A622266/NZIF_Radio/nzif/docs/NZIF_Radio_System_Architecture_Schematic_Review_2026-06-06.odt

NZIF Radio — System Architecture & Full Schematic Review

Review Date: 2026-06-06 | Scope: All schematic sheets, mixer-to-DSP core | Status: HOLD — Critical items block layout freeze

# 1. Executive Summary

This review covers the complete NZIF Radio schematic at the mixer-to-DSP level. Six domain expert reviews were conducted in parallel across all twelve schematic sheets. The design represents a genuinely novel 8-phase near-zero-IF architecture that is publishable in principle. However, the schematic has 11 Critical issues (up from 9 in the prior review), 25+ High issues, and numerous Moderate findings that must be resolved before layout or fabrication. Hardware does not yet exist; all performance figures are theoretical estimates requiring bring-up validation.

QST Verdict: The architecture deserves a QST article. The execution needs a complete schematic correction pass before that becomes possible. The minimum viable path to a working prototype requires resolution of all Tier 1 critical items listed in Section 6.

## 1.1 Top Critical Issues — Must Fix Before Layout

# | Sheet | Issue | Risk

CRITICAL 1 | rx_mixer rx_driver_amps | Wrong lib_ids on all custom power symbols (power:+5V used for −3.5V, +6.5V rails) | Netlist shorts negative op-amp rail to +5V; ADG884 destroyed on power-up
CRITICAL 2 | power_ldos | R903/R907/R908/R909 missing 'k' suffix (49.9 Ω not 49.9 kΩ) | All four LDO rails produce ~5 mV; complete subsystem failure
CRITICAL 3 | power_switching_reg | LT8330 feedback R1101/R1102 wrong values (produces −1.79V not −5V) | −5V rail absent; analog op-amp supply fails
CRITICAL 4 | power_switching_reg | ADP2303 R1103/R1104 wrong values (1.6V not target voltage) | Target rail at wrong voltage; dependent LDOs receive wrong input
CRITICAL 5 | clock_tree | R701 = 1 kΩ on OSC_CTRL; AD9523-1 requires ≥20 kΩ load (total 11 kΩ) | VCXO PLL1 will not lock; radio is inoperable without reference clock
CRITICAL 6 | clock_tree | U706 symbol=SN74CBT3253 (5V) vs. Value=SN74CBTLV3253 (3.6V max) | Wrong device assembled; 3.6V-max part destroyed at 5V supply
CRITICAL 7 | dacs | ADAU1962A AVDD driven from Q601 emitter follower: ~2.7V vs. 3.0V minimum | DAC internal references out of spec; possible startup failure
CRITICAL 8 | adcs audio_subsystem | Power symbol lib_id power:+3.3V used for +3.3V_CONVERTERS — merges with global +3.3V | ADC and ADAU1361 analog supply contaminated by digital noise; isolation defeated
CRITICAL 9 | audio_subsystem | Power symbol lib_id power:+5V for +3.3V_CONVERTERS — applies 5V to ADAU1361 IOVDD/AVDD (3.6V abs max) [NEW] | ADAU1361 destroyed on first power-up
CRITICAL 10 | audio_subsystem | Net label 'DVDOUT' should be 'DVDDOUT'; ADAU1361 internal LDO decoupling disconnected | Codec internal digital supply unstable; codec non-functional
CRITICAL 11 | adcs | ADAU1979 PLL_FILT cap C406 (5600 pF) marked DNP [NEW] | ADC internal PLL cannot lock; ADU1979 completely non-functional

# 2. System Architecture Assessment

## 2.1 Architecture Strengths

8-Phase Polyphase Mixer — Genuine Novelty: The 8-phase commutating topology with SN74CBT3125C bus switches provides theoretical >60 dB rejection of the 3rd LO harmonic, >50 dB of the 5th, and >45 dB of the 7th. No published amateur construction project has implemented this. The mathematics (8-point DFT phasor argument) is correct and is validated by the rxmixer.md simulation showing correct 45° phase spacing and matched amplitudes. This directly surpasses Tayloe's 4-phase detector (QEX, May 2001) and is the primary novelty claim for a QST article.

AD9523-1 Dual-Output Clock Architecture: Generating both the variable RF LO and the fixed audio MCLK from a single VCO, with the reference-path divider completely decoupled from PLL2 tuning, is architecturally elegant. Retuning the LO does not disturb the I2S clock domain — a non-trivial design insight that most amateur SDR designs get wrong. The AD9523-1's −226 dBc/Hz FOM is appropriate for a receiver targeting superheterodyne-class phase noise performance.

Ring Counter Phase Generation: The SN74AUC16374 ring counter producing eight non-overlapping phase pulses from a circulating single-bit shift register is original and elegant. The 4:1 mux initialisation sequence (clear → seed → run) reproducibly places exactly one '1' in the loop, solving the undefined power-up state problem without external reset logic. The 2.5V supply choice allows 237.6 MHz operation for 10m (8-phase) within the 250 MHz typical device rating.

Fully Differential Signal Flow: The receive chain is fully differential from the balun secondary through SN74CBT3125C switches → ADA4625-2 buffers → ADA4945-1 FDAs → ADAU1979 ADC. Maintaining differential mode throughout suppresses even-order nonlinearities and rejects common-mode RF interference. The LT5400 matched quad resistors for ADA4945-1 Rg positions (0.01% ratio matching, 0.5 ppm/°C tracking) are the right call for I/Q amplitude balance.

Near-Zero-IF + NCO Strategy: The ADAU1467 digital NCO (±96 kHz) offsets the receive center from DC, avoiding LO leakage and 1/f noise without a switched IF filter bank. Combined with 100 kHz LO steps from the AD9523-1, this provides continuous HF coverage. The Weaver two-stage demodulation (first stage: analog 8-phase mixer; second stage: digital NCO in ADAU1467) is a legitimate and clean implementation.

LT3045/LT3094 Power Architecture: The use of ultra-low-noise LDOs (2 µVrms) post-regulating from ADP2302/ADP2303 switchers, with domain-isolated rails for the clock tree, mixers, and audio converters, reflects serious attention to the ADC noise floor. The LT3045's 76 dB PSRR at 1 MHz directly addresses 700 kHz switcher ripple. This is a publishable design decision that most commercial SDR kits do not implement.

I/Q Calibration Architecture: The directional coupler calibration tap + HMC1118 switch injecting a known spectrally clean signal into the receive path for runtime I/Q calibration goes beyond any published amateur receiver design. If implemented correctly, this allows image rejection to be maintained across temperature and band changes without manual trimming.

ADAU1467 SigmaDSP Integration: The 294 MHz dual-core ADAU1467 running SigmaStudio graphical blocks (NCO, Weaver second stage, FIR/IIR filters, AGC, I/Q correction matrix) provides more DSP headroom than a comparably priced FPGA for audio-rate processing, without requiring custom firmware. I2C parameter RAM access from the Pico enables runtime calibration coefficient updates.

## 2.2 Architecture Concerns

TX Reconstruction Filter Absent [CRITICAL]: The tx_mixer.kicad_sch sheet title promises '16 Phase Tx Harmonic Mixer and Reconstruction Filter' but contains no filter components. DAC reconstruction images at LO ± 192 kHz and harmonics feed directly to the PA interface. The ZWAS LPF on the RF front-end board suppresses PA harmonics but not pre-PA mixer images. A fully differential LC filter at TX_RF+/TX_RF- is required before FCC Part 97 compliance can be claimed.

Hold Capacitor Values Produce ~4 kHz Baseband Bandwidth [NEW HIGH]: The rx_mixer annotation uses N=1 in the bandwidth equation; the correct value for an 8-phase topology is N=8. With 100 nF hold caps and Reff ≈ 50 Ω source / N=8: BW ≈ 1/(2π × 8 × 50 × 100 nF) ≈ 4 kHz. This is far below the ±96 kHz NCO range. For ±200 kHz bandwidth target: C_hold ≈ 2 nF. The current 100 nF caps limit the design to CW-only operation, inconsistent with the stated SSB/AM/digital mode goals.

VCXO vs. TCXO Conflict [NEW HIGH]: CLAUDE.md and the architecture description state CTS_535_TCXO as the frequency reference, but clock_tree.kicad_sch instantiates an ABLNO-V-VCXO. These are functionally different devices. The AD9523-1 is designed for a VCXO reference on PLL1 (OSC_CTRL drives Vc), which makes the ABLNO-VCXO the architecturally correct choice — but the documentation and schematic disagree. This must be resolved explicitly.

6m 4-Phase Mode Spurious Response: In 4-phase mode (6m), the 5th harmonic (f_LO/5 ≈ 10–10.8 MHz = 30m band) passes through with the same response vector as the fundamental. HP-2 (9 MHz cutoff) provides only modest attenuation at 10 MHz. Strong 30m signals will create interference on 6m. This limitation is inherent to 4-phase operation and should be quantified and disclosed in any QST article.

Power Sequencing Undefined: No PGOOD connections link switching regulator outputs to downstream LDO enable pins. The ADAU1467 requires DVDD and IOVDD within 0.3 V of each other during power-up to prevent latch-up. All rails currently rise simultaneously with no defined order. ADP2303 PGOOD pins have no pull-up resistors.

ADA4945-1 Feedback Caps All DNP: All eight 180 pF feedback capacitors across the ADA4945-1 Rf resistors are marked DNP. With Rf = 9.53 kΩ and no Cf, the ADA4945-1 will oscillate on first prototype, saturating all four differential channels and making the ADC input useless. These must be populated.

## 2.3 QST Readiness Assessment

Strengths for publication: The 8-phase polyphase mixer topology is a publishable concept that advances the state of amateur radio construction. The dual-path clock architecture, ring counter phase generation, and I/Q calibration system are all novel and technically rigorous. The LTspice simulation validating the 45° phase spacing is a publication-ready figure. A QST reviewer familiar with Tayloe's detector would immediately recognise this as a significant advancement.

Blockers to publication: (1) 11 critical schematic errors that would prevent a built board from functioning. (2) No hardware exists — all performance figures are theoretical estimates. QST requires bench-measured data for all performance claims. (3) TX reconstruction filter absent — transmitter cannot claim Part 97 compliance. (4) Hold capacitor values inconsistent with stated ±96 kHz operating bandwidth. (5) Schematic net errors (power symbol lib_ids) that would destroy components on first power-up.

Recommended path to QST submission: Fix all Tier 1 critical items → build first prototype → measure MDS, IIP3, harmonic rejection (3rd/5th/7th), image rejection, and TX spectrum → submit with measured data and corrected ERC-clean schematic.

# 3. New Findings — This Review Cycle

The following issues were not in the prior schematic_review_report.md and were identified by this review cycle:

Priority | Sheet | Ref/Net | Issue | Action
CRITICAL [NEW] | audio_subsystem | +3.3V_CONVERTERS power symbol | lib_id 'power:+5V' with Value '+3.3V_CONVERTERS' applies 5V to ADAU1361 IOVDD/AVDD (abs max 3.6V) → device destroyed | Create dedicated power symbol with lib_id 'power:+3.3V_CONVERTERS'
CRITICAL [NEW] | adcs | C406 (PLL_FILT) | 5600 pF PLL_FILT cap is marked DNP. ADAU1979 internal PLL cannot lock without this capacitor → ADC non-functional | Populate C406; do not DNP on prototype
CRITICAL [NEW] | dacs | Net '2.5' (no V suffix) | Label '2.5' (missing 'V') at line 6617 creates a net isolated from all '2.5V' nets. Floating node risk at DAC reference | Rename to '2.5V'; verify no other case/suffix mismatches in DAC sheet
HIGH [NEW] | clock_tree | X701 vs ABLNO-VCXO | Architecture docs say CTS_535_TCXO; schematic instantiates ABLNO-V-VCXO. Fundamentally different parts (TCXO vs VCXO) | Commit to ABLNO-VCXO (architecturally correct for AD9523-1 PLL1); update CLAUDE.md; remove unused CTS_535 symbol
HIGH [NEW] | rx_mixer | HC_201–208 hold caps | Bandwidth annotation uses N=1 but topology has N=8 phases. Correct BW with 100 nF: ~4 kHz, not 96 kHz. Inconsistent with ±96 kHz NCO design goal | Recalculate for N=8: C_hold ≈ 2 nF for 200 kHz target BW; update annotation and fitted values
HIGH [NEW] | adcs | U401 VREF buffer | R410 (3kΩ) loads ADAU1979 VREF pin (unbuffered bandgap output) with 0.83 mA before the ADA4807-1 buffer — exceeds recommended loading | Move R410 to output of ADA4807-1 buffer, not input; ensure VREF pin sees only buffer input impedance
HIGH [NEW] | adcs | C401, C403 AVDD caps | 10 µF AVDD bypass caps assigned to 0402 footprint. DC bias derating at 3.3V reduces effective C to 3–5 µF (marginal). No 10 µF ceramic exists in 1005 metric | Change footprint to 0805; use 10 µF X5R/X7R 0805 rated ≥6.3V
HIGH [NEW] | dacs | Q601 / AVDD | FZT951TA emitter follower produces ~3.3V − 0.6V = 2.7V AVDD at room temp. Falls further with temperature. ADAU1962A AVDD minimum is 3.0V | Replace Q601 with LT3045 LDO; set output to 3.3V with correct SET resistor value
HIGH [NEW] | dsp | SELFBOOT / U502 EEPROM | SELFBOOT pin state unconfirmed. U502 (25AA1024 SPI EEPROM) footprint is empty — absent from layout. Self-boot path cannot function without EEPROM | Assign footprint to U502; confirm SELFBOOT pulled high (IOVDD); document boot mode in schematic note
HIGH [NEW] | tx_mixer | Tx DAC differential polarity | DAC_N+/DAC_N− assignment to switch port A vs. B not verified. Any polarity reversal injects image/sideband rather than desired signal | Trace each DAC± to switch port; annotate polarity on schematic
MODERATE [NEW] | dsp | MiSO_M label | Label 'MiSO_M' (mixed case) creates a separate net from 'MISO_M' (all caps). KiCad net names are case-sensitive. ADAU1467 SPI EEPROM read path broken | Change 'MiSO_M' to 'MISO_M' throughout; verify with ERC
MODERATE [NEW] | audio_subsystem | C1215/C1216 footprint | 220 µF polarized electrolytic caps assigned to 0402 footprint (1.0×0.5 mm). No 220 µF ceramic exists in 0402. Assembly will fail | Change to through-hole radial or large-body SMD electrolytic footprint; consider 470 µF for fc ≈ 11 Hz
MODERATE [NEW] | tx_mixer clock_tree | Clock net naming inconsistency | clock_tree exports 'tx_phase_N'; tx_mixer imports 'CLK_N'; rx_mixer imports 'phase_N'. Three naming conventions for same signals | Standardise on one naming scheme across all sheets; verify all hierarchical connections are intact
MODERATE [NEW] | rx_driver_amps | ADA4945-1 VOCM pin | VOCM pin not explicitly driven. Default VOCM = midpoint of supply rails (+6.5V/−3.5V) = +1.5V. ADAU1979 VOCM = AVDD/2 = 1.65V. Marginal match, supply-dependent | Drive VOCM from resistor divider from ADAU1979 AVDD for stable common-mode matching
MODERATE [NEW] | power_switching_reg | ADP2303 bulk caps | Output bulk caps '47u 6.3V' — if used on 8V ADP2303 output (R1112/R1113), 6.3V rating exceeded | Verify which caps are on 8V output; replace with 47µF 16V-rated parts
MODERATE [NEW] | power_ldos | C913/C917/C922 '04.7u' notation | '04.7u' value notation on SET bypass caps is ambiguous; BOM tools may parse as 4.7 µF or 0.47 µF — 10× difference affects LDO PSRR | Change notation to '470n' (correct for SET pin bypass); or '4.7u' if bulk bypass is intended; confirm intent
MODERATE [NEW] | dsp | ADAU1467 per-pin decoupling | ADAU1467 has 17 separate power pins across 4 supply domains. Schematic must verify one 100 nF cap per physical pin at 294 MHz core clock frequency | Verify one decoupling cap per power pin on U501; ensure caps placed adjacent to each pin in layout

# 4. Status of Prior Review Issues

All items from the April 2026 review report (schematic_review_report.md) were re-evaluated against the current schematic. The following table summarises status:

Issue from Prior Report | Sheet | Prior Priority | Current Status
Wrong lib_ids on custom power symbols (−3.5V_RX_OPAMPS shorts to +5V/+6V global net) | rx_mixer rx_driver_amps | CRITICAL | OPEN — lib_id confirmed still wrong. ADG884 VDD on +3.3V_DSP_UC symbol resolves to +6V global net
R903/907/908/909 missing 'k' suffix (49.9 Ω not 49.9 kΩ) | power_ldos | CRITICAL | PARTIALLY FIXED — three other SET resistors corrected; four listed instances still at bare '49.9'
LT8330 R1101/R1102 wrong feedback (produces −1.79V not −5V) | power_switching_reg | CRITICAL | OPEN — R1101=1M, R1102=806k confirmed in schematic. Need R1101 = 4.22 MΩ for −5V
ADP2303 R1103/R1104 wrong values (1.6V not target) | power_switching_reg | CRITICAL | OPEN — both still 100kΩ → 1.6V. R1110/R1111, R1112/R1113 now populated correctly (6V, 8V rails)
R701 = 1kΩ on OSC_CTRL below 20kΩ min | clock_tree | CRITICAL | OPEN — R701 still reads '1k' in schematic
U706 SN74CBT3253/SN74CBTLV3253 part-value mismatch | clock_tree | CRITICAL | OPEN — symbol=SN74CBT3253, value=SN74CBTLV3253 mismatch still present
ADAU1962A AVDD 2.5V label (min 3.0V) | dacs | CRITICAL | OPEN — four '2.5V' labels in DAC sheet; Q601 emitter follower produces ~2.7V (below 3.0V min)
#PWR0406 power:+3.3V for +3.3V_CONVERTER rail | adcs | CRITICAL | OPEN — lib_id confirmed as power:+3.3V. Also #PWR0419, #PWR0420 same error

'DVDOUT' label should be 'DVDDOUT' (ADAU1361 LDO decoupling disconnected) | audio_subsystem | CRITICAL | OPEN — 'DVDOUT' still present at two locations in schematic
LT3045/LT3094 output caps 4.7µF (minimum 10µF for stability) | power_ldos | CRITICAL | OPEN — all LT3045 outputs still at 4.7µF; multiple confirmed instances. LDOs will oscillate
TX reconstruction filter absent despite sheet title promising it | tx_mixer | HIGH | OPEN — no filter components present on tx_mixer sheet
ADA4945-1 feedback caps all DNP (oscillation risk at 9.53kΩ Rf) | rx_driver_amps | HIGH | OPEN — all C343/C322/C319/C320/ C340/C341/C344 still marked DNP
R910 = 16.5kΩ produces 1.65V not 1.8V on clocktree rail | power_ldos | HIGH | OPEN — R910 still at 16.5kΩ; need 18.0kΩ for 1.8V
ADA4807-1 DISABLE pin unconfirmed | adcs | HIGH | OPEN — pin 5 has no connection
No differential shunt caps on AIN+/AIN− pairs | adcs | HIGH | OPEN — C405 (390pF) and C406 (5600pF) both DNP; no populated anti-aliasing cap on any AIN pair
PLL1 LF1_EXT_CAP not confirmed present | clock_tree | HIGH | OPEN — no cap confirmed on AD9523-1 pin 7 net
CTS 535 EOH and Vc not confirmed | clock_tree | HIGH | OPEN — EOH pin disposition unconfirmed; VCXO vs TCXO conflict newly identified
AD9523-1 ZD_IN/ZD_IN_b not terminated | clock_tree | HIGH | OPEN — pins 70/71 disposition not confirmed
I2S/TDM pull-up resistors not confirmed for ADAU1361 | audio_subsystem | HIGH | OPEN — no pull-ups found in audio_subsystem sheet
SSM2211S bulk bypass cap missing | audio_subsystem | HIGH | OPEN — only 100nF C1214 on 5V supply; need 10–47µF bulk
C623/C624/C628 value '0.iu' typo (unparseable by BOM tools) | dacs | CRITICAL | OPEN — confirmed still '0.iu' at three locations
ADP2303 PGOOD pins: no pull-ups | power_switching_reg | HIGH | OPEN — no pull-up resistors; no sequencing defined
ADP2303 inductors 3.3µH (datasheet recommends 4.7µH) | power_switching_reg | HIGH | OPEN — three instances still at '3.3u 3A'
Footprints missing on majority of passive components | all sheets | HIGH | PARTIALLY ADDRESSED — some footprints assigned; many still missing across all sheets

# 5. Per-Sheet Findings Summary

## 5.1 rx_mixer.kicad_sch — 8-Phase Receive Mixer

Priority | Finding
CRITICAL | All custom power symbols use lib_id power:+5V. −3.5V_RX_OPAMPS, +6.5V_RX_OPAMPS all resolve to global +5V net in netlist. ADA4625-2 negative supply and positive supply both shorted to +5V.
CRITICAL | SN74CBT3125CPW supply: Value now reads '+5V_RX_MIXER' (correct voltage for 5V device) but lib_id is power:+5V — merges with global +5V rather than an isolated mixer supply.
HIGH (NEW) | Hold cap bandwidth: 100 nF with N=8 phases gives BW ≈ 4 kHz, not 96 kHz as annotated (annotation uses N=1). Recalculate for N=8: C_hold ≈ 2 nF for ±200 kHz target.
MODERATE | ADA4625-2 exposed pad (EP, pin 9) not confirmed connected to V−. Required by datasheet; floating EP degrades thermal performance and substrate coupling between phase channels.
MODERATE | 10µF caps on +6.5V rail in 0603 package: 0603 ceramics typically rated ≤6.3V. Replace with 16V-rated 0805 parts.

## 5.2 rx_driver_amps.kicad_sch — Differential Driver Amplifiers

Priority | Finding
CRITICAL | All custom power rails use lib_id power:+6V. −3.5V_RX_OPAMPS, +6.5V_RX_OPAMPS, +3.3V_DSP_UC all resolve to global +6V net. ADG884 VDD (abs max 3.6V) shorted to +6V — device destroyed.
HIGH | ADA4945-1 feedback caps C343/C322/C319/C320/C340/C341/C344 all DNP. With Rf=9.53kΩ and no Cf, ADA4945-1 will oscillate. Must populate on first prototype.
HIGH (NEW) | Rf = 9.53kΩ contributes 12.6 nV/√Hz thermal noise at virtual ground node, dominating ADA4945-1's own 1.7 nV/√Hz. Consider reducing to 2–4kΩ range.
MODERATE (NEW) | ADA4945-1 VOCM pin not explicitly driven. Default VOCM = +1.5V (supply midpoint). ADAU1979 requires VOCM = AVDD/2 = 1.65V. Marginal match, supply-voltage dependent.
MODERATE | BB_0/BB_180 to P0_IN+/P0_IN− pairing not confirmed at top level. Incorrect I/Q phase assignment destroys image rejection.

## 5.3 clock_tree.kicad_sch — Phase Clock Generation

Priority | Finding
CRITICAL | R701 = 1kΩ on OSC_CTRL. AD9523-1 requires ≥20kΩ load at pin 8 (OSC_CTRL). Actual total: 10kΩ internal + 1kΩ = 11kΩ. PLL1 will not lock; radio inoperable.
CRITICAL | U706: symbol=SN74CBT3253 (5V), value=SN74CBTLV3253 (3.6V max). Wrong device assembled; 3.6V-max part destroyed at 5V supply, or 5V part produces wrong specifications.
HIGH (NEW) | VCXO vs. TCXO conflict: CLAUDE.md says CTS_535_TCXO; schematic instantiates ABLNO-V-VCXO. Commit to ABLNO-VCXO (correct for AD9523-1 PLL1); update documentation.
HIGH | PLL1 external loop filter cap (AD9523-1 pin 7, LF1_EXT_CAP) not confirmed present. PLL1 cannot lock without it.
HIGH | CTS 535 (or ABLNO-VCXO) EOH enable pin and Vc control not confirmed connected.
HIGH | AD9523-1 ZD_IN/ZD_IN_b (pins 70/71) not driven or terminated for zero-delay-bypass mode.
MODERATE | Frequency plan annotation absent from schematic. No divider settings, VCO frequencies, or output frequencies documented.
MODERATE | OSC_IN_b (AD9523-1 pin 10) AC-ground capacitor (100nF to GND) not confirmed for single-ended input mode.

## 5.4 adcs.kicad_sch — ADAU1979 ADC

Priority | Finding
CRITICAL | #PWR0406, #PWR0419, #PWR0420 all use lib_id power:+3.3V for +3.3V_CONVERTERS net. ADAU1979 AVDD merges with global +3.3V digital rail, defeating supply isolation.
CRITICAL (NEW) | C406 (5600pF, PLL_FILT) marked DNP. ADAU1979 internal PLL cannot lock without this external capacitor. ADC is completely non-functional.
HIGH (NEW) | R410 (3kΩ) loads ADAU1979 VREF pin (unbuffered bandgap output) with 0.83 mA before ADA4807-1 buffer. Correct topology: buffer first, then divide. VREF voltage may be pulled low.
HIGH | No differential shunt capacitors (100–470pF C0G) across any AIN+/AIN− pair. 10Ω series resistors alone provide no anti-aliasing or RF rejection.
HIGH | ADA4807-1 DISABLE (pin 5) has no connection. Active-low; floating may disable the amplifier.
HIGH (NEW) | 10µF AVDD caps C401/C403 assigned to 0402 footprint. DC bias derating reduces effective C to 3–5µF at 3.3V — marginal for ADAU1979. Use 0805 instead.
MODERATE | SA_MODE, ADDR0, ADDR1 pin levels not annotated. I2C address and serial interface mode undefined.

## 5.5 dacs.kicad_sch — ADAU1962A DAC

Priority | Finding
CRITICAL | ADAU1962A AVDD below 3.0V minimum. Q601 (FZT951TA) emitter follower produces ~3.3V − 0.6V = 2.7V at room temp; falls further with temperature. DAC out of spec.
CRITICAL | C623/C624/C628 have value '0.iu' — BOM tools cannot parse; capacitors will be omitted from build. Intended value: 100nF.
CRITICAL (NEW) | Net '2.5' (no V suffix) at line 6617 creates isolated net separate from '2.5V' nets. Floating node risk at DAC reference circuitry.
HIGH (NEW) | Q601 emitter-follower AVDD has no feedback regulation. Supply rejection is poor; DAC THD+N will be degraded from datasheet specification. Replace with LT3045 for correct AVDD.
MODERATE | R614 (IBIAS, 3.32kΩ) has no tolerance annotation. Must be 1% tolerance per datasheet. 5% substitution shifts DAC full-scale by ±5%.
MODERATE (NEW) | MCLK frequency not annotated. ADAU1962A requires MCLK ratio annotation (256× at 48kHz or 128× at 192kHz) to verify SigmaStudio configuration.

## 5.6 dsp.kicad_sch — ADAU1467 SigmaDSP

Priority | Finding
HIGH (NEW) | SELFBOOT pin state not documented. 25AA1024 SPI EEPROM (U502) has empty footprint field — absent from layout. Self-boot path non-functional without EEPROM on PCB.
MODERATE (NEW) | Label 'MiSO_M' (mixed case) creates separate net from 'MISO_M'. KiCad net names are case-sensitive. SPI EEPROM read path broken at this label.
MODERATE (NEW) | 17 ADAU1467 power pins across 4 supply domains require individual 100nF decoupling caps. Shared decoupling inadequate at 294 MHz core clock.
MODERATE (NEW) | ADAU1467 I2C address configuration not documented. SELFBOOT/ADDR pin states must be annotated; address collisions with ADAU1979, ADAU1962A, ADAU1361 must be ruled out.
MODERATE (NEW) | SigmaStudio project file not referenced from schematic. TDM slot assignments, MCLK ratio, NCO configuration cannot be verified by inspection.
MINOR | DSP_CLK (MCLK) frequency not annotated on schematic. Critical for SigmaStudio PLL configuration.

## 5.7 power_ldos.kicad_sch — LT3045/LT3094 LDOs

Priority | Finding
CRITICAL | R903/R907/R908/R909: value '49.9' without 'k' suffix = 49.9Ω → V_OUT ≈ 5mV on four LDO rails. Three other instances correctly read '49.9k'. Fix: add 'k' suffix to all four.
CRITICAL | All LT3045 output caps at 4.7µF (confirmed multiple instances). LT3045 datasheet requires minimum 10µF ceramic for stability. All LDOs will oscillate.
HIGH | R910 = 16.5kΩ → +1.8V_CLOCKTREE = 1.65V. Need 18.0kΩ for 1.8V output.
HIGH | LT3094 output cap C931 = 4.7µF (minimum 10µF required for stability).
MODERATE (NEW) | '04.7u' notation on two SET bypass caps is ambiguous. Correct to '470n' (intended value for LT3045 SET pin bypass per datasheet).
MODERATE | No ferrite bead between ADP2303 8V output and LT3045 input pins. 700kHz switcher ripple degrades LDO PSRR advantage.

## 5.8 power_switching_reg.kicad_sch — Switching Regulators

Priority | Finding
CRITICAL | LT8330 R1101 = 1MΩ produces −1.79V not −5V. Required: R1101 = 4.22MΩ (E96). Formula: R1 = R2 × (|Vout|/0.80V − 1) = 806k × 5.25 = 4.23MΩ.
CRITICAL | ADP2303 R1103/R1104 = 100k/100k produces 1.6V. Formula: Vout = 0.800 × (1 + RTOP/RBOT). For 4V: RTOP = 4 × RBOT = 400kΩ.
HIGH (NEW) | ADP2303 output bulk caps '47u 6.3V' — if on 8V output rail (R1112/R1113 instance), 6.3V rating is violated. Replace with 47µF 16V-rated on 8V rail.
HIGH | PGOOD pins on U1102/U1103/U1104 (ADP2303): no pull-up resistors and no no-connect markers. Power sequencing undefined.
HIGH | ADP2303 inductors: 3.3µH fitted vs. 4.7µH datasheet recommendation. Higher ripple current, saturation risk at full load.

## 5.9 audio_subsystem.kicad_sch — ADAU1361 Codec

Priority | Finding
CRITICAL | Net label 'DVDOUT' should be 'DVDDOUT'. ADAU1361 DVDDOUT (pin 24, internal 1.8V LDO output) drives the 'DVDDOUT' net; the 10µF decoupling caps are stranded on floating 'DVDOUT' net. Codec non-functional.
CRITICAL (NEW) | +3.3V_CONVERTERS power symbol uses lib_id power:+5V. Applies 5V to ADAU1361 IOVDD/AVDD (abs max 3.6V) → device destroyed on first power-up.
CRITICAL (NEW) | C1215/C1216 (220µF polarized) assigned to 0402 footprint. No 220µF ceramic in 0402 exists. Assembly will fail. Change to appropriate electrolytic/tantalum footprint.
HIGH | SSM2211S (U1202): only 100nF C1214 on V+ supply. Peak current ≈400mA requires 10–47µF bulk bypass.
MODERATE | RINP/RINN/RAUX (ADAU1361 pins 12/13/14) marked no_connect. Datasheet requires connection to CM. Floating analog inputs introduce noise into sigma-delta modulator.
MODERATE | JACKDET/MICIN (pin 4) marked no_connect. Floating digital input — add pull to defined level.
MODERATE | No RF EMI filter caps on any audio input. In RF radio environment, audio traces act as antennas. Add 100pF C0G to GND on each input.
MODERATE (NEW) | AMP_SHUTDOWN default pull-down not confirmed at signal source. SSM2211S should default to shutdown (safe) at power-up.

## 5.10 tx_mixer.kicad_sch — Transmit Mixer

Priority | Finding
HIGH | No reconstruction filter present despite sheet title 'Reconstruction Filter'. DAC images at LO ± 192kHz feed PA interface directly. Part 97 compliance cannot be claimed.
HIGH (NEW) | DAC_N+/DAC_N− differential polarity per switch arm not verified. Polarity reversal injects image instead of desired signal.
MODERATE | SN74CBT3125CPW symbol with Value 'SN74CBTLV3125' — BOM will pull wrong device (wrong voltage rating).
MODERATE | Duplicate hierarchical labels for all 8 CLK phases — benign if at different coordinates but creates ERC ambiguity; run ERC to confirm clean.
MODERATE (NEW) | Clock signal naming 'CLK_N' inconsistent with 'tx_phase_N' from clock_tree and 'phase_N' from rx_mixer. Verify all hierarchical connections are intact.

## 5.11 microcontroller.kicad_sch — Raspberry Pi Pico

Priority | Finding
MODERATE | Q501 USB_RESET circuit incomplete (acknowledged in schematic note). Complete or document replacement approach before fabrication.
MODERATE | SWIO_0–3 hierarchical labels have no defined destination or purpose annotation. Add hierarchical labels and document SWIO_VLOGIC source voltage.
MODERATE | MCP23017 GPA7/GPB7 must be outputs only (silicon errata). Confirm schematic and planned firmware enforce this.
MINOR | ADAU1467 I2C/SPI address configuration not cross-referenced from this sheet. Verify address conflicts with other I2C devices are ruled out.

# 6. Prioritized Action Plan

## 6.1 Tier 1 — Block Layout: Must Fix First

All Tier 1 actions must be completed and verified before committing to PCB stackup.

# | Action | Owner | Sheets

T1-1 | Fix ALL power symbol lib_ids in rx_mixer.kicad_sch and rx_driver_amps.kicad_sch. Create dedicated symbols for −3.5V_RX_OPAMPS, +6.5V_RX_OPAMPS, +5V_RX_MIXER, +3.3V_DSP_UC with matching lib_ids. Regenerate netlist; verify zero cross-connections in ERC. | RF | rx_mixer rx_driver_amps
T1-2 | Correct all LT3045/LT3094 SET resistors: add 'k' suffix to R903, R907, R908, R909 (49.9Ω → 49.9kΩ). Verify each LT3045 output voltage against target. Fix R910 to 18.0kΩ for +1.8V_CLOCKTREE. | Power | power_ldos
T1-3 | Replace all LT3045/LT3094 output capacitors from 4.7µF to ≥10µF ceramic (X5R/X7R, 0805, adequate voltage derating). Verify C931 (LT3094 output) also replaced. | Power | power_ldos
T1-4 | Recalculate switching regulator feedback resistors: R1101 → 4.22MΩ (LT8330 for −5V); R1103 → 402kΩ (ADP2303 for target voltage). Verify all six populated resistors (R1108–R1113) produce correct output voltages. | Power | power_switching_reg
T1-5 | Fix R701 on OSC_CTRL: change from 1kΩ to ≥10kΩ (making total load ≥20kΩ) to meet AD9523-1 minimum. Document OSC_CTRL loading calculation on schematic. | Clock | clock_tree
T1-6 | Resolve U706 part/value conflict. Commit to SN74CBT3253 (5V) for Tx mux; update symbol lib_id, value, footprint, and BOM entry consistently. Also resolve VCXO vs. TCXO conflict: commit to ABLNO-VCXO; update CLAUDE.md. | Clock | clock_tree
T1-7 | Fix ADAU1962A AVDD supply: replace Q601 (FZT951TA emitter follower producing ~2.7V) with LT3045 LDO set to 3.3V. Fix '0.iu' typo on C623/C624/C628 → '100n'. Rename '2.5' net label → '2.5V'. | Precision | dacs
T1-8 | Fix ADC power symbols: replace power:+3.3V lib_id on #PWR0406, #PWR0419, #PWR0420 with dedicated +3.3V_CONVERTERS power symbol to preserve rail isolation. | Precision | adcs
T1-9 | Fix audio_subsystem power symbols: replace power:+5V lib_id on '+3.3V_CONVERTERS' symbol (applies 5V to ADAU1361 3.6V-max supply). Create dedicated symbol with correct lib_id. | Audio | audio_subsystem
T1-10 | Rename 'DVDOUT' → 'DVDDOUT' in audio_subsystem.kicad_sch (two instances). Run ERC to confirm CM and DVDDOUT nets are distinct. | Audio | audio_subsystem
T1-11 | Populate C406 (5600pF, ADAU1979 PLL_FILT): remove DNP marker. ADC is non-functional with this cap absent. | Precision | adcs
T1-12 | Correct hold cap values: recalculate for N=8 phases. For ±200kHz BW: C_hold ≈ 2nF. Update all HC_201–HC_208 values and correct N annotation from N=1 to N=8 in the design note. | RF | rx_mixer

## 6.2 Tier 2 — Fix Before PCB Stackup Decisions

# | Action | Owner | Sheets

T2-1 | Fix ADAU1979 VREF buffer topology: move R410 (3kΩ) to ADA4807-1 output, not VREF pin input. Ensure ADA4807-1 DISABLE pin tied to V+. | Precision | adcs
T2-2 | Populate ADA4945-1 feedback caps (180pF): remove DNP from C343/C322/C319/C320/C340/C341/C344. Do not DNP on first prototype with 9.53kΩ Rf. | RF | rx_driver_amps
T2-3 | Add TX reconstruction filter at TX_RF+/TX_RF- output. Design 7-element differential LC Chebyshev with passband edge at ~300kHz, stopband at ~192kHz. | RF/System | tx_mixer nzif
T2-4 | Confirm/add PLL1 loop filter cap (AD9523-1 pin 7, LF1_EXT_CAP) per datasheet recommendation. Drive EOH on VCXO to enable state. Terminate ZD_IN/ZD_IN_b. | Clock | clock_tree
T2-5 | Connect OSC_IN_b (AD9523-1 pin 10) to AC ground via 100nF cap for single-ended input mode. | Clock | clock_tree
T2-6 | Add frequency plan annotation table in clock_tree.kicad_sch: reference frequency, PLL1/PLL2 VCO frequencies, all divider settings, resulting output frequencies. | Clock | clock_tree
T2-7 | Confirm ADAU1467 SELFBOOT pin pulled high (IOVDD). Assign footprint to U502 (25AA1024 SPI EEPROM) — must appear in layout for self-boot. | DSP | dsp
T2-8 | Fix 'MiSO_M' label (mixed case) → 'MISO_M' throughout dsp.kicad_sch. Run ERC to confirm zero label case conflicts. | DSP | dsp
T2-9 | Add PGOOD pull-ups (100kΩ) on ADP2303 PGOOD pins. Define power sequencing: connect PGOOD outputs to downstream LDO EN pins or add sequencer IC. | Power | power_switching_reg power_ldos
T2-10 | Replace 0402 footprint on C1215/C1216 (220µF) with appropriate electrolytic/tantalum footprint. Consider 470µF for fc ≈ 11Hz margin. | Audio | audio_subsystem
T2-11 | Drive ADA4945-1 VOCM pin from AVDD/2 resistor divider to match ADAU1979 common-mode input requirement (1.65V at 3.3V AVDD). | RF | rx_driver_amps
T2-12 | Resolve VCXO vs TCXO conflict (document in T1-6); update CLAUDE.md to match schematic component selection. | System | clock_tree
T2-13 | Verify each of 17 ADAU1467 power pins has individual 100nF decoupling cap placed adjacent in layout. | DSP | dsp
T2-14 | Standardise clock signal naming across all sheets (tx_phase_N vs CLK_N vs phase_N). Verify all hierarchical connections intact after rename. | System | tx_mixer clock_tree rx_mixer
T2-15 | Verify Tx DAC differential polarity: trace each DAC_N+/DAC_N− to switch port; annotate polarity on tx_mixer schematic. | RF | tx_mixer

## 6.3 Tier 3 — Complete Before Final ERC Sign-Off

# | Action | Owner | Sheets

T3-1 | Assign all missing component footprints across all sheets. Priority: U401 (ADA4807-1), X701/ABLNO-VCXO, U704/U707 (SN74LVC8T245), C401/C403 (change to 0805 as per T2), all remaining passive footprints. | All | all sheets
T3-2 | Add anti-aliasing caps (100–470pF C0G) across each AIN+/AIN− pair at ADAU1979 inputs. Remove DNP from C405/C406 per T1-11. | Precision | adcs
T3-3 | Connect RINP/RINN/RAUX (ADAU1361 pins 12/13/14) to CM net instead of no_connect. Add pull to defined level on JACKDET/MICIN (pin 4). | Audio | audio_subsystem
T3-4 | Add bulk bypass cap (10–47µF) on SSM2211S V+ supply (pin 6). Change C1212 from 0.47µF to 1µF (SSM2211S BYPASS pin recommendation). | Audio | audio_subsystem
T3-5 | Add RF EMI filter caps (100pF C0G to GND) on all audio input traces at MIC_IN, Line_Input hierarchical label pins. | Audio | audio_subsystem
T3-6 | Add ADA4625-2 EP (pin 9) connection to V− supply rail in rx_mixer.kicad_sch for all 8 instances. | RF | rx_mixer
T3-7 | Replace 10µF 0603 caps on +6.5V rail with 16V-rated 0805 parts in rx_mixer.kicad_sch. | RF | rx_mixer
T3-8 | Add ferrite bead + 10µF cap between ADP2303 8V output and LT3045 input pins. Restore LDO PSRR advantage at 700kHz. | Power | power_ldos
T3-9 | Complete Q501 USB_RESET circuit or document alternative; remove incomplete schematic note. | uC | microcontroller
T3-10 | Resolve SWIO_0–3 destinations; annotate SWIO_VLOGIC source voltage; define pin purpose. | uC | microcontroller nzif
T3-11 | Annotate ADAU1467 and ADAU1979 I2C addresses on respective sheets. Document I2S/TDM mode (TDM4 vs TDM8) and slot assignments for both ICs. Reference SigmaStudio project location. | DSP Precision | dsp adcs dacs
T3-12 | Add AMP_SHUTDOWN pull-down to GND at source (microcontroller or top-level). SSM2211S must default to shutdown on power-up. | Audio | audio_subsystem microcontroller
T3-13 | Confirm I2C pull-up resistors (2kΩ to IOVDD) exist at exactly one point in hierarchy for each I2C bus: ADAU1361, ADAU1467, ADAU1979, ADAU1962A, MCP23017. | System | all sheets
T3-14 | Correct '04.7u' notation on LT3045 SET bypass caps to '470n' (unambiguous). Verify all LT3045 SET pin bypass caps are populated. | Power | power_ldos
T3-15 | Run full ERC with zero errors and zero warnings as gate criterion for layout freeze. | All | all sheets

# 7. Theoretical Performance Analysis

## 7.1 Receive Signal Chain — Dynamic Range Estimate

All figures are theoretical estimates. Hardware bring-up measurements are required.

Noise floor: Mixer conversion loss ≈ 6 dB. ADA4625-2 contributes ≈ 2–3 dB NF. ADA4945-1 with Rf = 9.53kΩ contributes 12.6 nV/√Hz Johnson noise (dominant). Total estimated system NF = 6–9 dB.

ADC chain dynamic range: ADAU1979 full-scale = 4.5 Vrms differential. ADA4945-1 noise floor ≈ 3.1 µVrms (over 192kHz BW). Theoretical dynamic range ≈ 123 dB. Practical expectation: 110–115 dB (limited by ADC quantization + ADA4945-1 noise).

Harmonic rejection (theoretical): 3rd LO harmonic: >60 dB. 5th: >50 dB. 7th: >45 dB. Practical expectation for well-built board: 40–55 dB (limited by switch Rds(on) matching and phase-clock timing accuracy).

Hold cap bandwidth note [CRITICAL DESIGN ISSUE]: Current 100nF hold caps with N=8 phases produce ≈4 kHz baseband bandwidth. This limits the receiver to CW-only operation and is inconsistent with the stated ±96 kHz NCO range. Recalculate for N=8: C_hold ≈ 2 nF for ±200 kHz target BW.

Metric | NZIF (estimated) | NC2030 (measured) | Notes
System NF | 6–9 dB | ~12 dB | NZIF: no on-board LNA; figures unverified
System IIP3 | +25–35 dBm | +28.5 dBm | NZIF: SN74CBT3125 not characterised as RF mixer; must measure
Harmonic rejection (3rd/5th/7th) | 40–55 dB (est.) | >45 dB (phasing) | NZIF: phase-clock timing accuracy is limiting factor
Instantaneous BW | ±96 kHz (target) ≈4 kHz (current caps) | ~1.5 kHz | NZIF hold caps must be changed to 2nF for target BW
ADC SNR | 110–115 dB (192kHz) | N/A | ADAU1979 specification; supply quality critical
DAC THD+N | <0.005% (target) | N/A | ADAU1962A spec; degraded by Q601 unregulated AVDD
MDS at ±96kHz BW | ~−115 dBm (est.) | −135 dBm @ 500Hz BW | Bandwidth-corrected comparison: NZIF ~−109 dBm equivalent

# 8. Path to QST Publication

## 8.1 What Would Impress QST Reviewers

• 8-phase polyphase commutating mixer: novel at amateur level, directly extending Tayloe's 4-phase detector (QEX May 2001) to 8-phase with harmonic rejection to the 7th LO harmonic. Phasor mathematics and LTspice simulation are publication-ready.

• AD9523-1 dual-output clock architecture: LO tuning without disturbing the audio clock domain is a non-trivial insight not seen in amateur SDR designs.

• SN74AUC16374 ring counter phase generation: elegant, reproducible single-bit shift register producing eight non-overlapping phases from a high-speed clock.

• Fully differential signal flow through LT5400 matched-quad resistors for I/Q amplitude balance.

• Weaver two-stage demodulation: first stage in analog 8-phase mixer, second stage in ADAU1467 digital NCO — clean and technically rigorous.

• I/Q calibration via directional coupler calibration tap: more sophisticated than any published amateur receiver design.

• LT3045/LT3094 power architecture: 2 µVrms noise floor, domain-isolated rails — publishable design decision that most commercial SDR kits skip.

• ZWAS quasi-elliptic LPF bank serving dual TX/RX purpose: the trap that rejects the 2nd PA harmonic on transmit is the same trap that notches the adjacent amateur band on receive.

## 8.2 What Would Concern QST Reviewers

• TX reconstruction filter absent: transmitter cannot demonstrate Part 97 compliance. Mandatory before any submission.

• No measured performance data: all figures are theoretical estimates. QST requires bench-measured MDS, IIP3, harmonic rejection, and image rejection.

• 11 critical schematic errors: any one would prevent a built board from functioning. Schematics must be ERC-clean before submission.

• Hold capacitor design error (N=8 vs N=1): ≈4 kHz bandwidth vs stated ±96 kHz. A reviewer will check this calculation.

• ADAU1467 is a 300-ball BGA: home construction requires professional PCB assembly. Note assembly requirements clearly.

• SigmaStudio proprietary toolchain: reviewer may ask whether design is replicable without purchasing SigmaStudio license. Provide .dspproj file.

• 6m 4-phase spurious response to 30m signals: must be quantified and disclosed in article.

• Power supply bring-up risk (LDOs oscillate due to insufficient output capacitance, switcher feedback values wrong) means average builder may not diagnose failures.

## 8.3 Minimum Viable Path to Submission

• Step 1: Week 1: Complete all Tier 1 critical schematic fixes (T1-1 through T1-12).

• Step 2: Week 2: Complete Tier 2 items, particularly TX reconstruction filter design (T2-3) and AD9523-1 configuration (T2-4–T2-6).

• Step 3: Week 3: Assign all footprints, run ERC to zero errors, freeze schematic for layout.

• Step 4: Layout: Length-match all phase_0...phase_315 traces. Isolate clock tree from baseband. Follow LT3045 layout guidelines for output cap placement.

• Step 5: Bring-up: Measure and document: (1) All supply rail voltages with oscilloscope for LDO stability, (2) AD9523-1 lock status, (3) ADAU1979 and ADAU1962A I2C communication, (4) ADAU1467 program load verification.

• Step 6: Performance measurements: MDS (Y-factor or noise source comparison), two-tone IIP3, harmonic rejection at f_LO/3, f_LO/5, f_LO/7, image rejection, TX spectrum (with reconstruction filter).

• Step 7: Submission: Corrected ERC-clean schematic, SigmaStudio project file, AD9523-1 register dump, measured performance data table, Pico firmware source.

NZIF Radio Schematic Review — Generated 2026-06-06 | Reviewers: HF Architecture, RF Mixer, Clock Tree, Power/Audio, Precision Analog, Audio Subsystem | Status: HOLD — 11 Critical items block layout freeze
