A622266/NZIF_Radio/nzif/nzif_3D_models/SOIC-16_ONS.step

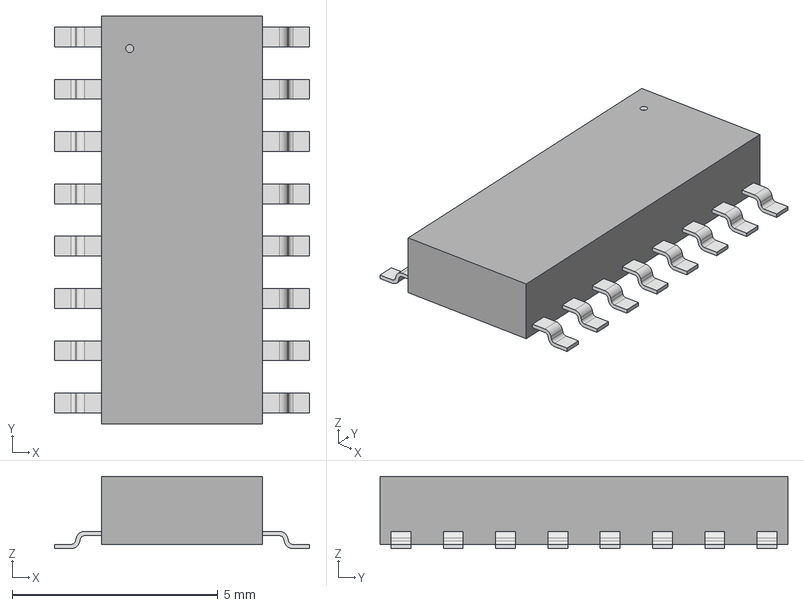
[picture p51: CAD file, 2026-01-13]
nzif/nzif_3D_models/SOIC-16_ONS.step
6.20 x 9.91 x 1.75 mm
