A622266/NZIF_Radio/nzif/nzif_3D_models/SOT223-FZT690B-DN_DIO.step

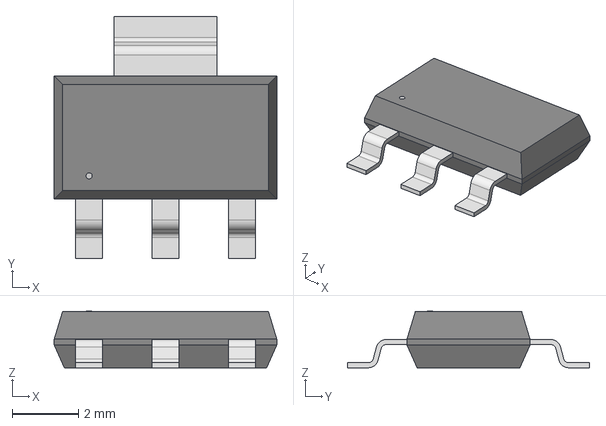
[picture p52: CAD file, 2026-01-13]
nzif/nzif_3D_models/SOT223-FZT690B-DN_DIO.step
6.71 x 7.29 x 1.70 mm
