A622266/NZIF_Radio/nzif/nzif_3D_models/PW0016A.stp

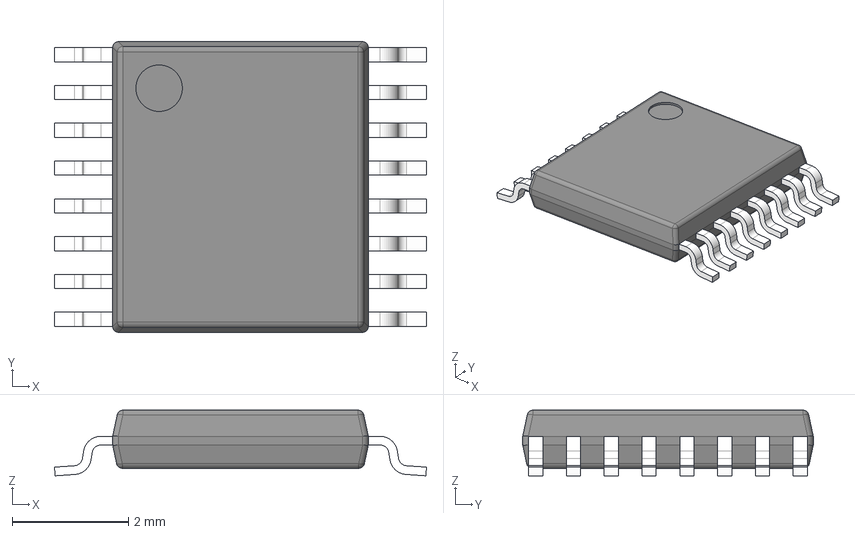
[picture p53: CAD file, 2026-01-11]
nzif/nzif_3D_models/PW0016A.stp
6.40 x 5.00 x 1.13 mm
BODY-TSSOP
LEAD-TSSOP x 16
PIN1
