A622266/NZIF_Radio/nzif/nzif_3D_models/DD_05-08-1725_ADI.step

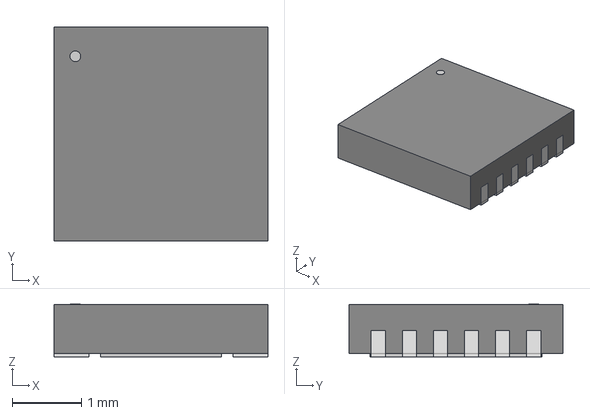
[picture p54: CAD file, 2026-01-10]
nzif/nzif_3D_models/DD_05-08-1725_ADI.step
3.10 x 3.10 x 0.765 mm
