A622266/NZIF_Radio/nzif/nzif_3D_models/CP-72-6_ADI.step

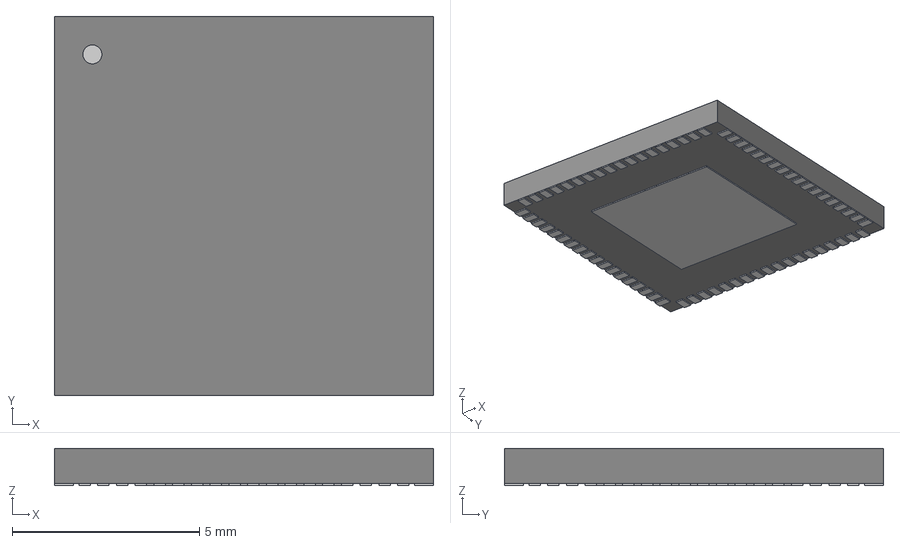
[picture p55: CAD file, 2026-01-10]
nzif/nzif_3D_models/CP-72-6_ADI.step
10.1 x 10.1 x 0.993 mm
