A622266/NZIF_Radio/nzif/nzif_3D_models/PW0014A.stp

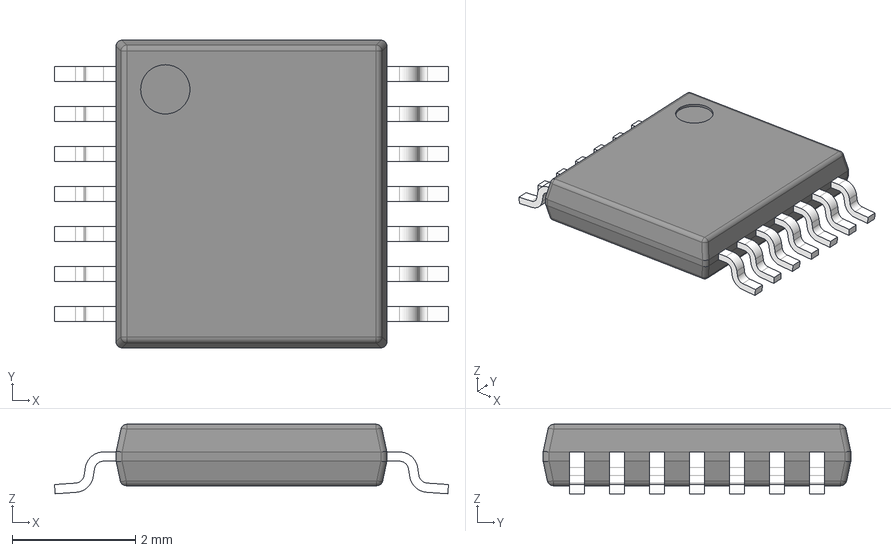
[picture p56: CAD file, 2026-01-10]
nzif/nzif_3D_models/PW0014A.stp
6.40 x 5.00 x 1.13 mm
BODY-TSSOP
LEAD-TSSOP x 14
PIN1
