A622266/NZIF_Radio/nzif/nzif_3D_models/MSOP-8_MS_LIT.step

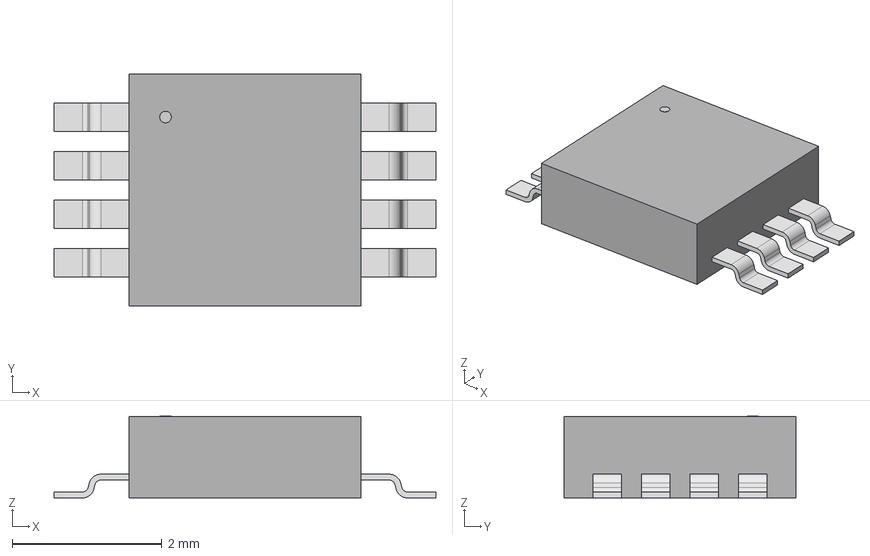
[picture p57: CAD file, 2026-01-10]
nzif/nzif_3D_models/MSOP-8_MS_LIT.step
5.11 x 3.10 x 1.09 mm
