A622266/NZIF_Radio/nzif/nzif_3D_models/LFCSP16_ADA4945-1ACPZ-R2_ADI.step

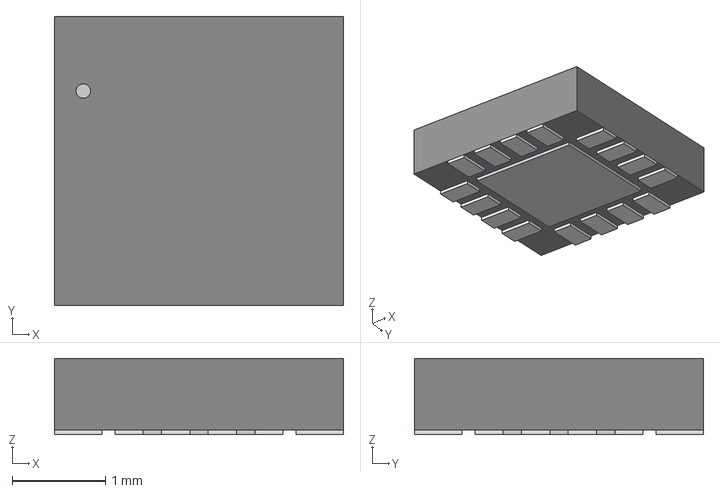
[picture p58: CAD file, 2026-01-10]
nzif/nzif_3D_models/LFCSP16_ADA4945-1ACPZ-R2_ADI.step
3.10 x 3.10 x 0.815 mm
