A622266/NZIF_Radio/nzif/nzif_3D_models/SOT-23_S6_LIT.step

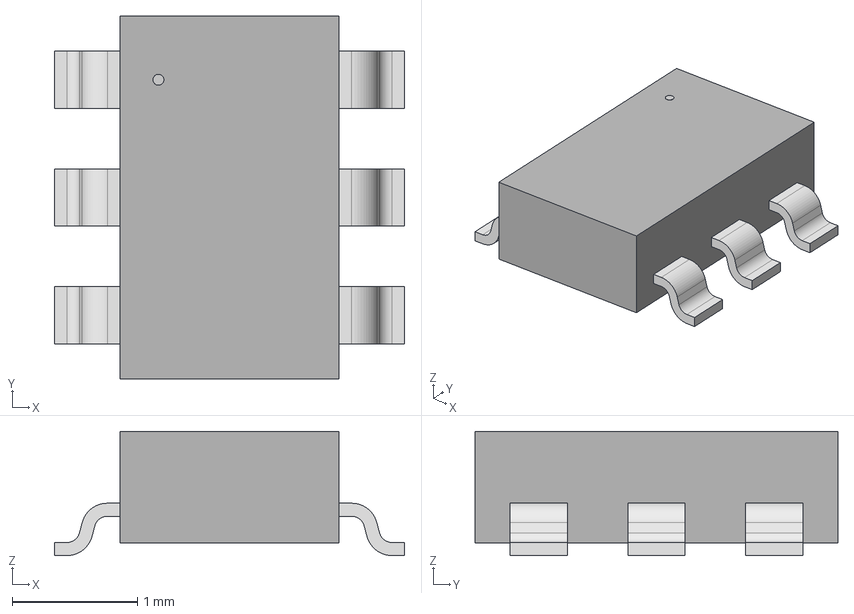
[picture p59: CAD file, 2026-01-10]
nzif/nzif_3D_models/SOT-23_S6_LIT.step
2.79 x 2.90 x 0.993 mm
