A622266/NZIF_Radio/nzif/nzif_3D_models/DFN-S8_6x5MC_MCH.step

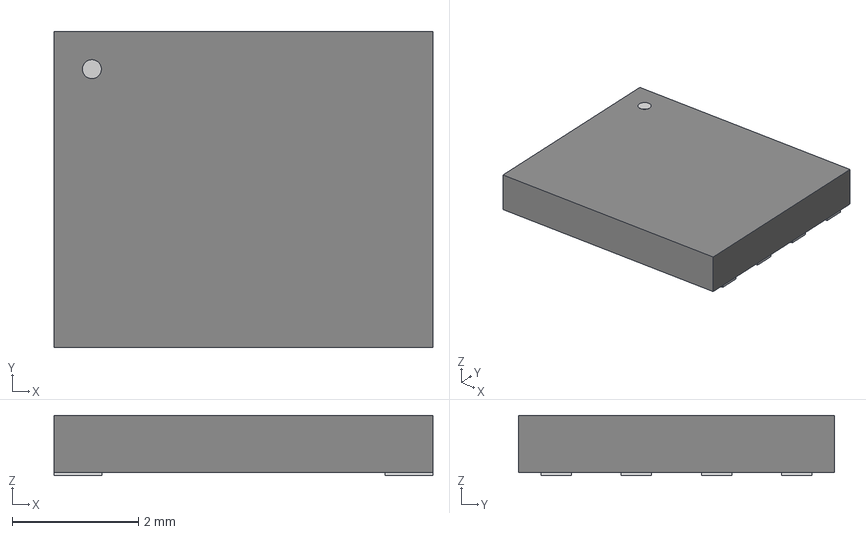
[picture p60: CAD file, 2026-01-10]
nzif/nzif_3D_models/DFN-S8_6x5MC_MCH.step
6.00 x 5.00 x 0.952 mm
