A622266/NZIF_Radio/nzif/nzif_3D_models/RA_4_ADI.step

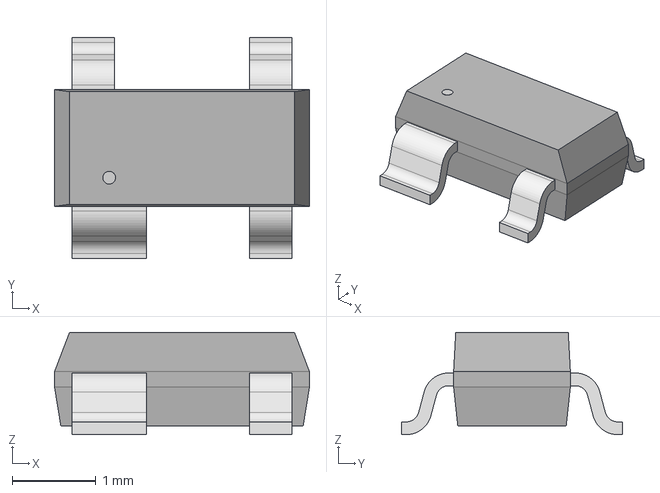
[picture p61: CAD file, 2026-01-10]
nzif/nzif_3D_models/RA_4_ADI.step
3.05 x 2.64 x 1.22 mm
