A622266/NZIF_Radio/nzif/nzif_3D_models/DPAK_TO-252__TYPEA_STM.step

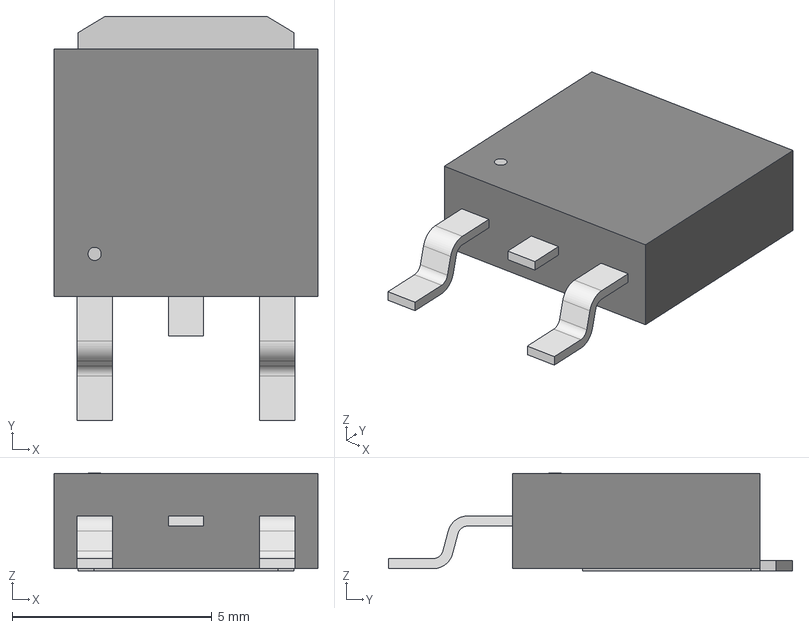
[picture p62: CAD file, 2026-01-10]
nzif/nzif_3D_models/DPAK_TO-252__TYPEA_STM.step
6.60 x 10.1 x 2.44 mm
