A622266/NZIF_Radio/nzif/nzif_3D_models/CP_88_8_ADI.step

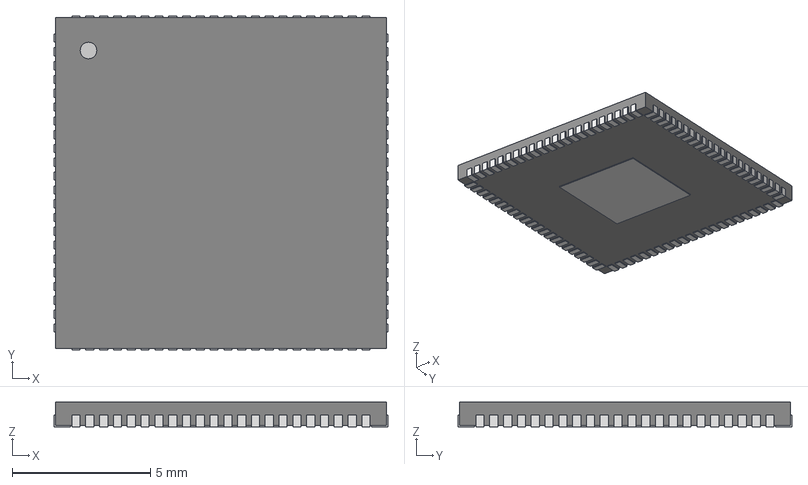
[picture p63: CAD file, 2026-01-07]
nzif/nzif_3D_models/CP_88_8_ADI.step
12.1 x 12.1 x 0.903 mm
