A622266/NZIF_Radio/nzif/nzif_3D_models/DBV0005A.stp

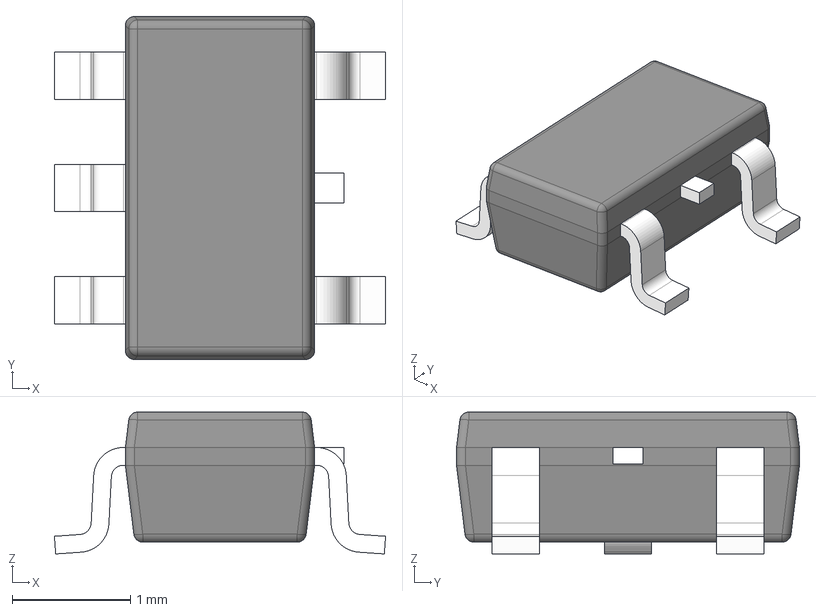
[picture p64: CAD file, 2026-01-05]
nzif/nzif_3D_models/DBV0005A.stp
2.80 x 2.90 x 1.20 mm
BODY-SOT
LEAD-SOT x 5
LEAD-DUMMY
