A622266/NZIF_Radio/nzif/nzif_3D_models/CP-32-4_ADI.step

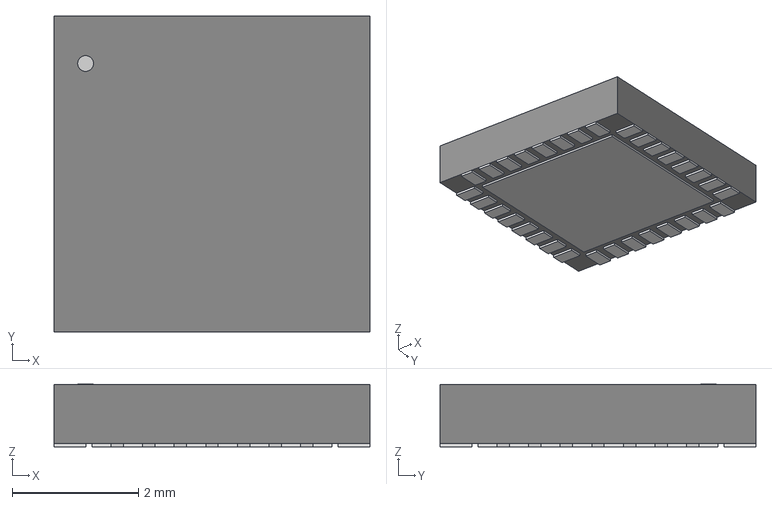
[picture p65: CAD file, 2026-01-05]
nzif/nzif_3D_models/CP-32-4_ADI.step
5.00 x 5.00 x 0.993 mm
