A622266/NZIF_Radio/nzif/nzif_3D_models/CP_24_7_ADI.step

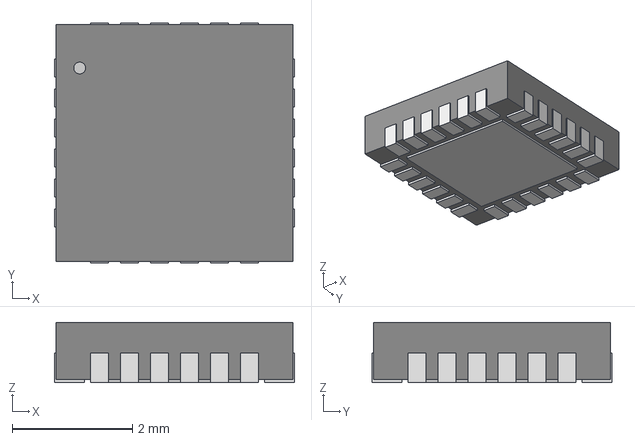
[picture p66: CAD file, 2026-01-05]
nzif/nzif_3D_models/CP_24_7_ADI.step
4.00 x 4.00 x 1.00 mm
