A622266/NZIF_Radio/nzif/nzif_3D_models/RM_8_ADI.step

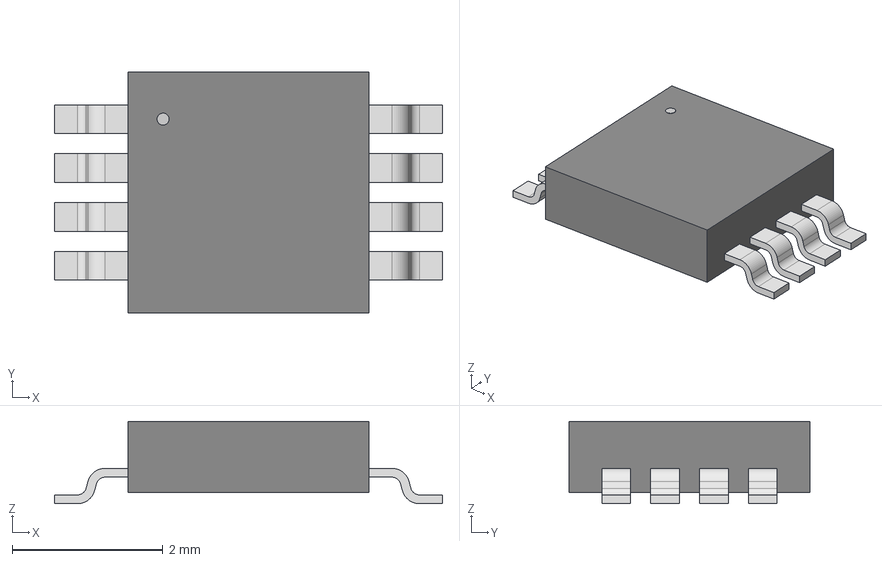
[picture p67: CAD file, 2026-01-05]
nzif/nzif_3D_models/RM_8_ADI.step
5.16 x 3.20 x 1.09 mm
