A622266/NZIF_Radio/nzif/nzif_3D_models/ST_80_2_ADI.step

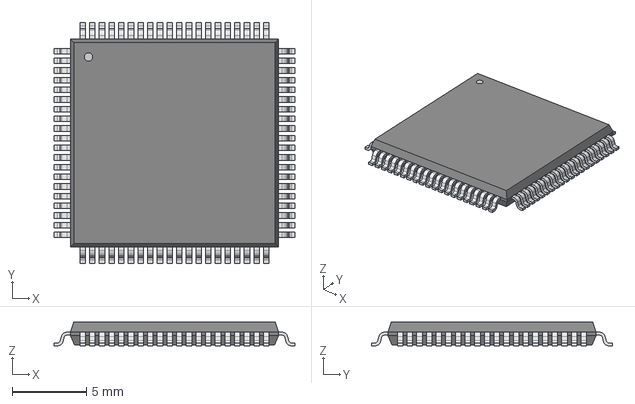
[picture p68: CAD file, 2026-01-05]
nzif/nzif_3D_models/ST_80_2_ADI.step
16.2 x 16.2 x 1.60 mm
