A622266/NZIF_Radio/spice_models/models/adg719_test.asc

B1: bv; V={Vpk*sin(2*pi*(fLO+fa)*time)}
C1: cap; 10µ
C2: cap; 10µ
C3: cap; 4.7n
C4: cap; 4.7n
Lp: ind; 4µ; Rser=1m
Ls1: ind; 1µ; Rser=1m
Ls2: ind; 1µ; Rser=1m
R1: res; 100Meg
R2: res; 100Meg
R3: res; 50
R4: res; 100
R5: res; 100
R6: res; 47
R7: res; 47
U1: ADG719
U3: ADG719
U5: UniversalOpAmp
U6: UniversalOpAmp
V1: voltage; 5
V2: voltage; PULSE(0 5 {Th} 5n 5n {Th} {T})
V5: voltage; PULSE(0 5 0 5n 5n {Th} {T})
V6: voltage; -12
V7: voltage; 12
Named nets: 5, 0, CLK_180, CLK_0, RF+, Ant, baseband_180, RF-, -12, 12, baseband_0
K Lp Ls1 Ls2 1
.options method=gear
; ===== LO PARAMETERS =====
.param fLO = 3.5Meg
.param fa = 1k
.param T   = 1/fLO
.param Th  = T/2
.save V(ant) V(rf+) V(rf-) V(baseband_0) V(baseband_180) V(clk_0) V(clk_180)
;======= Amplitude Parameters =======
.param Pin_dBm = -73
.param Rsrc = 50
.param Pwatts = 10^((Pin_dBm-30)/10)
.param Vrms = sqrt(Pwatts*Rsrc)
.param Vpk = sqrt(2)*Vrms
;.op
;meas op VPK_FIND FIND V(VPK_NODE)
.tran 0 2m 0 10n
.param Vpk = 70u
