A622266/NZIF_Radio/spice_models/models/sn74cbt3125c/sn74cbt3125_test.asc

B1: bv; V=V(carrier)+V(audio)
C1: cap; 10µ
C3: cap; 1µ
R2: res; 100Meg
U3: ADG719
V1: voltage; 5
V2: voltage; PULSE(0 3.3 0 1n 1n 50n 500n)
V3: voltage; SINE(0 70u 2Meg); Rser=50
V4: voltage; SINE(0 70u 2k); Rser=50
Named nets: 5, 0, baseband_0, CLK_0, carrier, audio, RF+
.lib EPCGaNLibrary.lib
; 10 MHz clock, 50% duty, 1 ns rise/fall
.tran 0 5m 0 10u
