A622266/NZIF_Radio/spice_models/models/epc2037_4_channel.asc

B1: bv; V={Vpk*sin(2*pi*(fLO+fa)*time)}
C1: cap; 100n
C2: cap; 47n
C6: cap; 1µ
R3: res; 100Meg
R5: res; 3
R9: res; 100k
S1: sw; SWMOD
U1: opamp
U4: lmg1020
V1: voltage; 5
V2: voltage; PULSE(0 5 0 1n 1n {T/4} {T})
V3: voltage; PULSE(0 5 {T/4} 1n 1n {T/4} {T})
V4: voltage; PULSE(0 5 {T/2} 1n 1n {T/4} {T})
V5: voltage; PULSE(0 5 {3*T/4} 1n 1n {T/4} {T})
Named nets: 0, VDD, RF, CLK180, CLK90, BB_0, CLK0, CLK270
.tran 0 4m 0 2n
.options method=gear
.lib opamp.sub
; ===== LO PARAMETERS =====
.param fLO=10Meg
.param fa = 1k
.param T   = 1/fLO
.param Th  = T/2
.param Vpk=6
.inc lmg1020.lib
.inc EPCGaNLibrary.lib
.model SWMOD SW(Ron=0.1 Roff=1Meg Vt=2.5 Vh=0)
