A622266/NZIF_Radio/spice_models/models/sn74cbt3125c_4_channel.asc

B1: bv; V={Vpk*sin(2*pi*(fLO+fa)*time)}
C1: cap; 10µ
C2: cap; 47n
C3: cap; 47n
C4: cap; 47n
C5: cap; 47n
R1: res; 100Meg
R2: res; 100Meg
R3: res; 100Meg
R4: res; 100Meg
U1: opamp
U2: opamp
U3: opamp
U4: sn74cbt3125casy
U5: opamp
V1: voltage; 5
V2: voltage; PULSE(0 5 0 1n 1n {T/4} {T})
V3: voltage; PULSE(0 5 {T/4} 1n 1n {T/4} {T})
V4: voltage; PULSE(0 5 {T/2} 1n 1n {T/4} {T})
V5: voltage; PULSE(0 5 {3*T/4} 1n 1n {T/4} {T})
Named nets: 0, 5, RF, CLK180, CLK0, CLK90, BB_0, BB_90, BB_180, BB_270, CLK270
.tran 0 4m 0 2n
.options method=gear
.include sn74cbt3125c.sub
.lib opamp.sub
; ===== LO PARAMETERS =====
.param fLO=10Meg
.param fa = 1k
.param T   = 1/fLO
.param Th  = T/2
.param Vpk=4
0, 45, 90, 135, 180, 225, 270 315
