A622266/NZIF_Radio/spice_models/models/sn74cbt3125c_8_channel.asc

B1: bv; V={Vpk*sin(2*pi*(fLO+fa)*time)}
C1: cap; 10µ
C2: cap; 47n
C3: cap; 47n
C4: cap; 47n
C5: cap; 47n
C6: cap; 47n
C7: cap; 47n
C8: cap; 47n
C9: cap; 47n
L1: ind; 4µ; Rser=1m
L2: ind; 4µ; Rser=1m
L3: ind; 4µ; Rser=1m
R1: res; 100Meg
R2: res; 100Meg
R3: res; 100Meg
R4: res; 100Meg
R5: res; 100Meg
R6: res; 100Meg
R7: res; 100Meg
R8: res; 100Meg
U1: opamp
U2: opamp
U3: opamp
U4: sn74cbt3125casy
U5: opamp
U6: sn74cbt3125casy
U7: opamp
U8: opamp
U9: opamp
U10: opamp
V1: voltage; 5
V2: voltage; PULSE(0 5 0 1n 1n {T/2} {T})
V3: voltage; PULSE(0 5 {T/8} 1n 1n {T/2} {T})
V4: voltage; PULSE(0 5 {T/4} 1n 1n {T/2} {T})
V5: voltage; PULSE(0 5 {3*T/8} 1n 1n {T/2} {T})
V6: voltage; PULSE(0 5 {5*T/8} 1n 1n {T/2} {T})
V7: voltage; PULSE(0 5 {3*T/4} 1n 1n {T/2} {T})
V8: voltage; PULSE(0 5 {T/2} 1n 1n {T/2} {T})
V9: voltage; PULSE(0 5 {7*T/8} 1n 1n {T/2} {T})
V10: voltage; 2.5
Named nets: 0, 5, ANT, RF+, CLK90, CLK0, CLK45, BB_0, BB_45, BB_90, BB_135, CLK135, CLK270, CLK225, CLK180, CLK315, RF-, BB_180, BB_225, BB_270, BB_315
.tran 0 4m 0 2n
.options method=gear
.include sn74cbt3125c.sub
.lib opamp.sub
; ===== LO PARAMETERS =====
.param fLO=30Meg
.param fa = 1k
.param T   = 1/fLO
.param Th  = T/2
.param Vpk=5m
((v(bb_0)-2.5)+(v(bb_180)-2.5)+(sqrt(2)/2)*((v(bb_45)-2.5)+(v(bb_225)-2.5)-(v(bb_135)-2.5)-(v(bb_315)-2.5)))/2.828
((v(bb_90)-2.5)+(v(bb_270)-2.5)+(sqrt(2)/2)*((v(bb_45)-2.5)+(v(bb_225)-2.5)+(v(bb_135)-2.5)+(v(bb_315)-2.5)))/2.828
Clocks
K L1 L2 L3 1
.param Vbias = 2.5
