A622266/NZIF_Radio/spice_models/models/lt3042/lt3042.asc

C1: cap; 4.7µ
C2: cap; 4.7µ
C3: cap; .47µ
R1: res; 49.9k
U1: LT3042
V1: voltage; 5.5
Named nets: 0, 5V_mixer, 5.5V
.tran 0 1 0 5u startup
